gonium/EVSE-Car-Simulator/doc/img/pcb-rendering.png

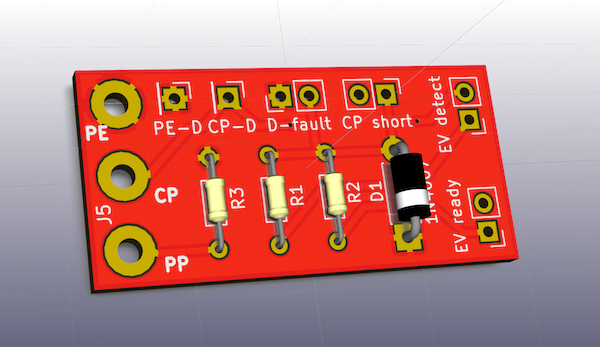
doc/img/pcb-rendering.png
