gonium/EVSE-Car-Simulator/doc/img/platine-header.jpg

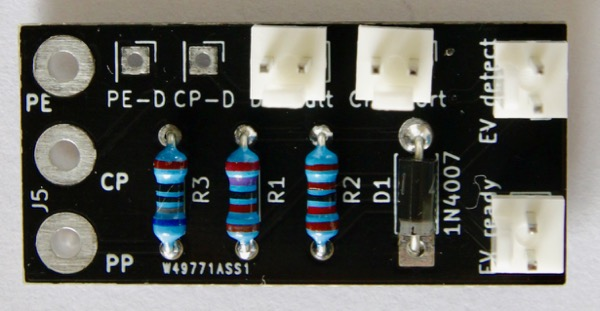
doc/img/platine-header.jpg
