gonium/EVSE-Car-Simulator/doc/img/vehicle-detected.png

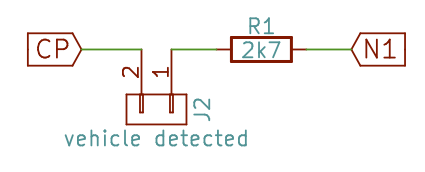
doc/img/vehicle-detected.png
